elektrojupp/AD9954_TESTBOARD/pictures/IMG_0599.jpg

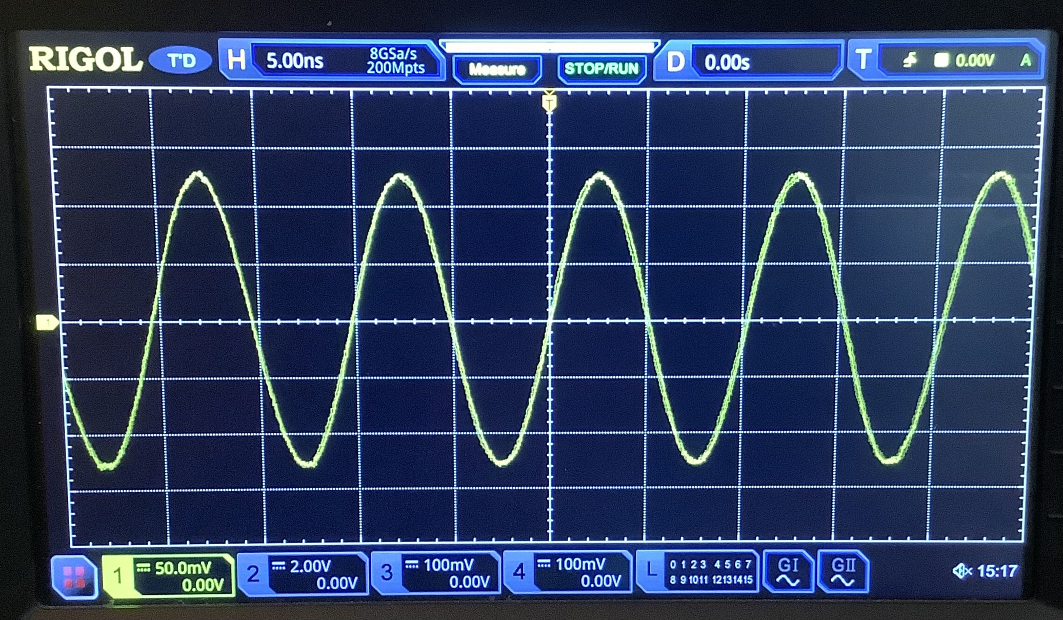
pictures/IMG_0599.jpg
