elektrojupp/AD9954_TESTBOARD/pictures/IMG_E0605.JPG

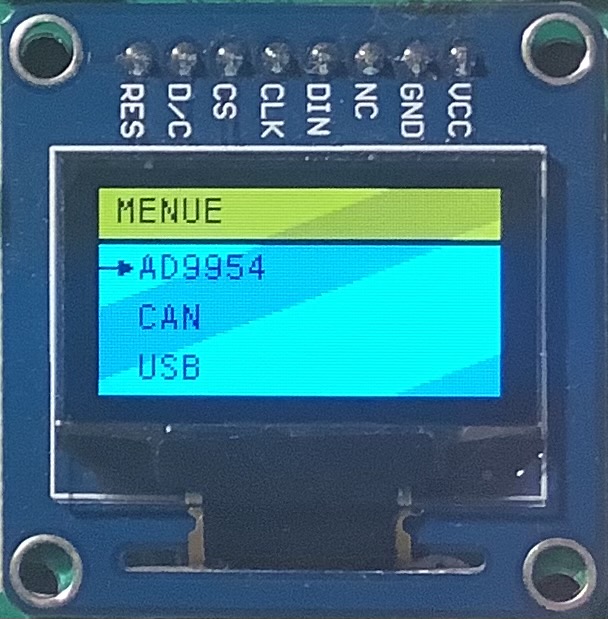
pictures/IMG_E0605.JPG
