elektrojupp/AD9954_TESTBOARD/pictures/IMG_E0612.JPG

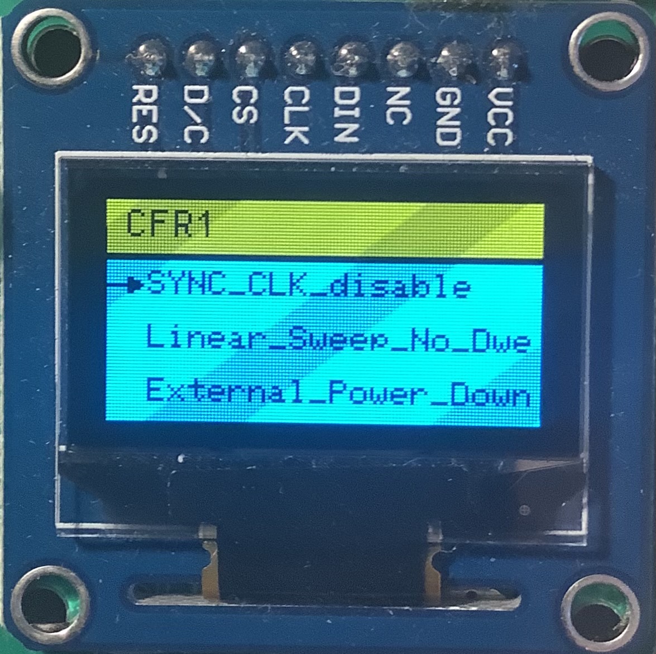
pictures/IMG_E0612.JPG
