elektrojupp/AD9954_TESTBOARD/pictures/IMG_E0613.JPG

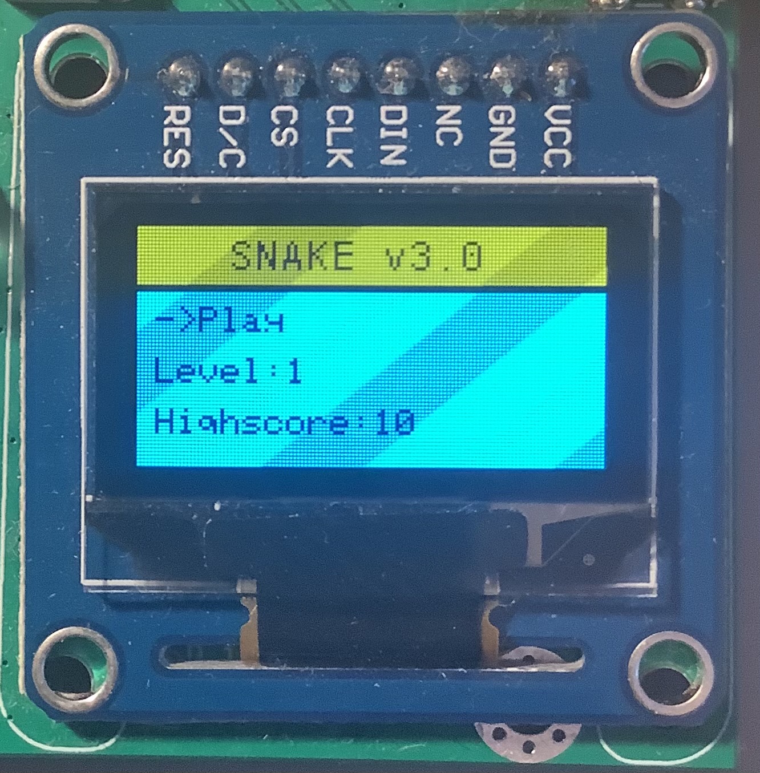
pictures/IMG_E0613.JPG
