elektrojupp/AD9954_TESTBOARD/pictures/IMG_E0616.JPG

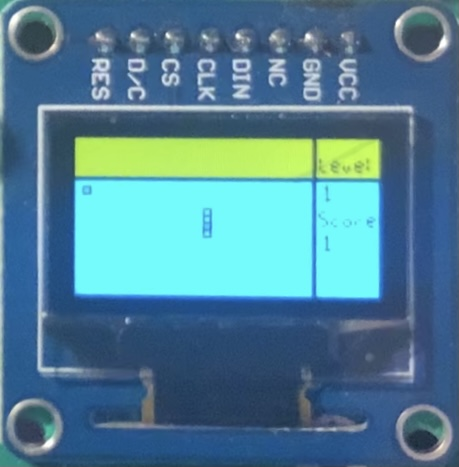
pictures/IMG_E0616.JPG
