elektrojupp/AD9954_TESTBOARD/pictures/IMG_E0635.JPG

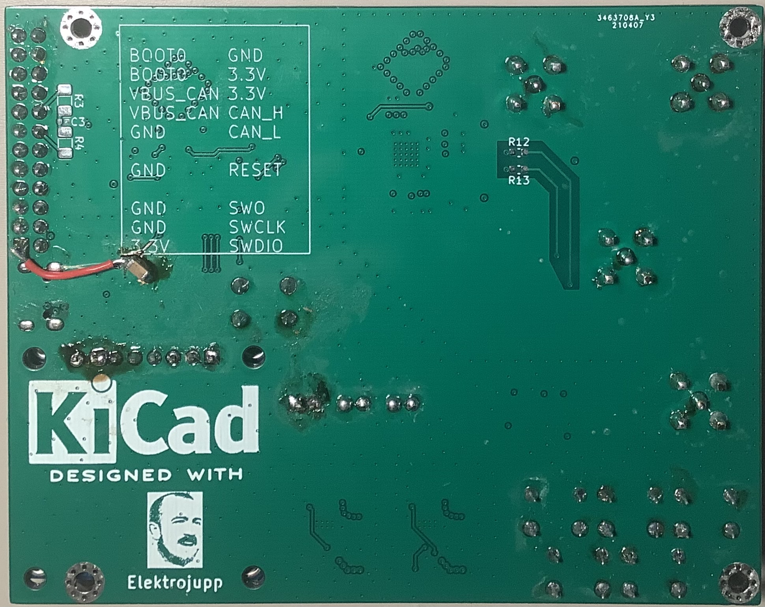
pictures/IMG_E0635.JPG
