elektrojupp/AD9954_TESTBOARD/software/Core/Inc/eeprom.h

#ifndef __EEPROM_H
#define __EEPROM_H

#ifdef __cplusplus
extern "C" {
#endif

#include <inttypes.h>

void EEPROM_Read(uint8_t adr, uint8_t * data, uint8_t size);
void EEPROM_Write(uint16_t adr, uint8_t * values, uint16_t size);



// FIRST BANK

#define ADDR_FLASH_PAGE_0     ((uint32_t)0x08000000) /* Base @ of Page 0, 2 Kbytes */
#define ADDR_FLASH_PAGE_1     ((uint32_t)0x08000800) /* Base @ of Page 1, 2 Kbytes */
#define ADDR_FLASH_PAGE_2     ((uint32_t)0x08001000) /* Base @ of Page 2, 2 Kbytes */
#define ADDR_FLASH_PAGE_3     ((uint32_t)0x08001800) /* Base @ of Page 3, 2 Kbytes */
#define ADDR_FLASH_PAGE_4     ((uint32_t)0x08002000) /* Base @ of Page 4, 2 Kbytes */
#define ADDR_FLASH_PAGE_5     ((uint32_t)0x08002800) /* Base @ of Page 5, 2 Kbytes */
#define ADDR_FLASH_PAGE_6     ((uint32_t)0x08003000) /* Base @ of Page 6, 2 Kbytes */
#define ADDR_FLASH_PAGE_7     ((uint32_t)0x08003800) /* Base @ of Page 7, 2 Kbytes */
#define ADDR_FLASH_PAGE_8     ((uint32_t)0x08004000) /* Base @ of Page 8, 2 Kbytes */
#define ADDR_FLASH_PAGE_9     ((uint32_t)0x08004800) /* Base @ of Page 9, 2 Kbytes */
#define ADDR_FLASH_PAGE_10     ((uint32_t)0x08005000) /* Base @ of Page 10, 2 Kbytes */
#define ADDR_FLASH_PAGE_11     ((uint32_t)0x08005800) /* Base @ of Page 11, 2 Kbytes */
#define ADDR_FLASH_PAGE_12     ((uint32_t)0x08006000) /* Base @ of Page 12, 2 Kbytes */
#define ADDR_FLASH_PAGE_13     ((uint32_t)0x08006800) /* Base @ of Page 13, 2 Kbytes */
#define ADDR_FLASH_PAGE_14     ((uint32_t)0x08007000) /* Base @ of Page 14, 2 Kbytes */
#define ADDR_FLASH_PAGE_15     ((uint32_t)0x08007800) /* Base @ of Page 15, 2 Kbytes */
#define ADDR_FLASH_PAGE_16     ((uint32_t)0x08008000) /* Base @ of Page 16, 2 Kbytes */
#define ADDR_FLASH_PAGE_17     ((uint32_t)0x08008800) /* Base @ of Page 17, 2 Kbytes */
#define ADDR_FLASH_PAGE_18     ((uint32_t)0x08009000) /* Base @ of Page 18, 2 Kbytes */
#define ADDR_FLASH_PAGE_19     ((uint32_t)0x08009800) /* Base @ of Page 19, 2 Kbytes */
#define ADDR_FLASH_PAGE_20     ((uint32_t)0x0800a000) /* Base @ of Page 20, 2 Kbytes */
#define ADDR_FLASH_PAGE_21     ((uint32_t)0x0800a800) /* Base @ of Page 21, 2 Kbytes */
#define ADDR_FLASH_PAGE_22     ((uint32_t)0x0800b000) /* Base @ of Page 22, 2 Kbytes */
#define ADDR_FLASH_PAGE_23     ((uint32_t)0x0800b800) /* Base @ of Page 23, 2 Kbytes */
#define ADDR_FLASH_PAGE_24     ((uint32_t)0x0800c000) /* Base @ of Page 24, 2 Kbytes */
#define ADDR_FLASH_PAGE_25     ((uint32_t)0x0800c800) /* Base @ of Page 25, 2 Kbytes */
#define ADDR_FLASH_PAGE_26     ((uint32_t)0x0800d000) /* Base @ of Page 26, 2 Kbytes */
#define ADDR_FLASH_PAGE_27     ((uint32_t)0x0800d800) /* Base @ of Page 27, 2 Kbytes */
#define ADDR_FLASH_PAGE_28     ((uint32_t)0x0800e000) /* Base @ of Page 28, 2 Kbytes */
#define ADDR_FLASH_PAGE_29     ((uint32_t)0x0800e800) /* Base @ of Page 29, 2 Kbytes */
#define ADDR_FLASH_PAGE_30     ((uint32_t)0x0800f000) /* Base @ of Page 30, 2 Kbytes */
#define ADDR_FLASH_PAGE_31     ((uint32_t)0x0800f800) /* Base @ of Page 31, 2 Kbytes */
#define ADDR_FLASH_PAGE_32     ((uint32_t)0x08010000) /* Base @ of Page 32, 2 Kbytes */
#define ADDR_FLASH_PAGE_33     ((uint32_t)0x08010800) /* Base @ of Page 33, 2 Kbytes */
#define ADDR_FLASH_PAGE_34     ((uint32_t)0x08011000) /* Base @ of Page 34, 2 Kbytes */
#define ADDR_FLASH_PAGE_35     ((uint32_t)0x08011800) /* Base @ of Page 35, 2 Kbytes */
#define ADDR_FLASH_PAGE_36     ((uint32_t)0x08012000) /* Base @ of Page 36, 2 Kbytes */
#define ADDR_FLASH_PAGE_37     ((uint32_t)0x08012800) /* Base @ of Page 37, 2 Kbytes */
#define ADDR_FLASH_PAGE_38     ((uint32_t)0x08013000) /* Base @ of Page 38, 2 Kbytes */
#define ADDR_FLASH_PAGE_39     ((uint32_t)0x08013800) /* Base @ of Page 39, 2 Kbytes */
#define ADDR_FLASH_PAGE_40     ((uint32_t)0x08014000) /* Base @ of Page 40, 2 Kbytes */
#define ADDR_FLASH_PAGE_41     ((uint32_t)0x08014800) /* Base @ of Page 41, 2 Kbytes */
#define ADDR_FLASH_PAGE_42     ((uint32_t)0x08015000) /* Base @ of Page 42, 2 Kbytes */
#define ADDR_FLASH_PAGE_43     ((uint32_t)0x08015800) /* Base @ of Page 43, 2 Kbytes */
#define ADDR_FLASH_PAGE_44     ((uint32_t)0x08016000) /* Base @ of Page 44, 2 Kbytes */
#define ADDR_FLASH_PAGE_45     ((uint32_t)0x08016800) /* Base @ of Page 45, 2 Kbytes */
#define ADDR_FLASH_PAGE_46     ((uint32_t)0x08017000) /* Base @ of Page 46, 2 Kbytes */
#define ADDR_FLASH_PAGE_47     ((uint32_t)0x08017800) /* Base @ of Page 47, 2 Kbytes */
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
#define ADDR_FLASH_PAGE_228     ((uint32_t)0x08072000) /* Base @ of Page 228, 2 Kbytes */
#define ADDR_FLASH_PAGE_229     ((uint32_t)0x08072800) /* Base @ of Page 229, 2 Kbytes */
#define ADDR_FLASH_PAGE_230     ((uint32_t)0x08073000) /* Base @ of Page 230, 2 Kbytes */
#define ADDR_FLASH_PAGE_231     ((uint32_t)0x08073800) /* Base @ of Page 231, 2 Kbytes */
#define ADDR_FLASH_PAGE_232     ((uint32_t)0x08074000) /* Base @ of Page 232, 2 Kbytes */
#define ADDR_FLASH_PAGE_233     ((uint32_t)0x08074800) /* Base @ of Page 233, 2 Kbytes */
#define ADDR_FLASH_PAGE_234     ((uint32_t)0x08075000) /* Base @ of Page 234, 2 Kbytes */
#define ADDR_FLASH_PAGE_235     ((uint32_t)0x08075800) /* Base @ of Page 235, 2 Kbytes */
#define ADDR_FLASH_PAGE_236     ((uint32_t)0x08076000) /* Base @ of Page 236, 2 Kbytes */
#define ADDR_FLASH_PAGE_237     ((uint32_t)0x08076800) /* Base @ of Page 237, 2 Kbytes */
#define ADDR_FLASH_PAGE_238     ((uint32_t)0x08077000) /* Base @ of Page 238, 2 Kbytes */
#define ADDR_FLASH_PAGE_239     ((uint32_t)0x08077800) /* Base @ of Page 239, 2 Kbytes */
#define ADDR_FLASH_PAGE_240     ((uint32_t)0x08078000) /* Base @ of Page 240, 2 Kbytes */
#define ADDR_FLASH_PAGE_241     ((uint32_t)0x08078800) /* Base @ of Page 241, 2 Kbytes */
#define ADDR_FLASH_PAGE_242     ((uint32_t)0x08079000) /* Base @ of Page 242, 2 Kbytes */
#define ADDR_FLASH_PAGE_243     ((uint32_t)0x08079800) /* Base @ of Page 243, 2 Kbytes */
#define ADDR_FLASH_PAGE_244     ((uint32_t)0x0807a000) /* Base @ of Page 244, 2 Kbytes */
#define ADDR_FLASH_PAGE_245     ((uint32_t)0x0807a800) /* Base @ of Page 245, 2 Kbytes */
#define ADDR_FLASH_PAGE_246     ((uint32_t)0x0807b000) /* Base @ of Page 246, 2 Kbytes */
#define ADDR_FLASH_PAGE_247     ((uint32_t)0x0807b800) /* Base @ of Page 247, 2 Kbytes */
#define ADDR_FLASH_PAGE_248     ((uint32_t)0x0807c000) /* Base @ of Page 248, 2 Kbytes */
#define ADDR_FLASH_PAGE_249     ((uint32_t)0x0807c800) /* Base @ of Page 249, 2 Kbytes */
#define ADDR_FLASH_PAGE_250     ((uint32_t)0x0807d000) /* Base @ of Page 250, 2 Kbytes */
#define ADDR_FLASH_PAGE_251     ((uint32_t)0x0807d800) /* Base @ of Page 251, 2 Kbytes */
#define ADDR_FLASH_PAGE_252     ((uint32_t)0x0807e000) /* Base @ of Page 252, 2 Kbytes */
#define ADDR_FLASH_PAGE_253     ((uint32_t)0x0807e800) /* Base @ of Page 253, 2 Kbytes */
#define ADDR_FLASH_PAGE_254     ((uint32_t)0x0807f000) /* Base @ of Page 254, 2 Kbytes */
#define ADDR_FLASH_PAGE_255     ((uint32_t)0x0807f800) /* Base @ of Page 255, 2 Kbytes */

// SECOND BANK

#define ADDR_FLASH_PAGE_256     ((uint32_t)0x08080000) /* Base @ of Page 256, 2 Kbytes */
#define ADDR_FLASH_PAGE_257     ((uint32_t)0x08080800) /* Base @ of Page 257, 2 Kbytes */
#define ADDR_FLASH_PAGE_258     ((uint32_t)0x08081000) /* Base @ of Page 258, 2 Kbytes */
#define ADDR_FLASH_PAGE_259     ((uint32_t)0x08081800) /* Base @ of Page 259, 2 Kbytes */
#define ADDR_FLASH_PAGE_260     ((uint32_t)0x08082000) /* Base @ of Page 260, 2 Kbytes */
#define ADDR_FLASH_PAGE_261     ((uint32_t)0x08082800) /* Base @ of Page 261, 2 Kbytes */
#define ADDR_FLASH_PAGE_262     ((uint32_t)0x08083000) /* Base @ of Page 262, 2 Kbytes */
#define ADDR_FLASH_PAGE_263     ((uint32_t)0x08083800) /* Base @ of Page 263, 2 Kbytes */
#define ADDR_FLASH_PAGE_264     ((uint32_t)0x08084000) /* Base @ of Page 264, 2 Kbytes */
#define ADDR_FLASH_PAGE_265     ((uint32_t)0x08084800) /* Base @ of Page 265, 2 Kbytes */
#define ADDR_FLASH_PAGE_266     ((uint32_t)0x08085000) /* Base @ of Page 266, 2 Kbytes */
#define ADDR_FLASH_PAGE_267     ((uint32_t)0x08085800) /* Base @ of Page 267, 2 Kbytes */
#define ADDR_FLASH_PAGE_268     ((uint32_t)0x08086000) /* Base @ of Page 268, 2 Kbytes */
#define ADDR_FLASH_PAGE_269     ((uint32_t)0x08086800) /* Base @ of Page 269, 2 Kbytes */
#define ADDR_FLASH_PAGE_270     ((uint32_t)0x08087000) /* Base @ of Page 270, 2 Kbytes */
#define ADDR_FLASH_PAGE_271     ((uint32_t)0x08087800) /* Base @ of Page 271, 2 Kbytes */
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
#define ADDR_FLASH_PAGE_484     ((uint32_t)0x080f2000) /* Base @ of Page 484, 2 Kbytes */
#define ADDR_FLASH_PAGE_485     ((uint32_t)0x080f2800) /* Base @ of Page 485, 2 Kbytes */
#define ADDR_FLASH_PAGE_486     ((uint32_t)0x080f3000) /* Base @ of Page 486, 2 Kbytes */
#define ADDR_FLASH_PAGE_487     ((uint32_t)0x080f3800) /* Base @ of Page 487, 2 Kbytes */
#define ADDR_FLASH_PAGE_488     ((uint32_t)0x080f4000) /* Base @ of Page 488, 2 Kbytes */
#define ADDR_FLASH_PAGE_489     ((uint32_t)0x080f4800) /* Base @ of Page 489, 2 Kbytes */
#define ADDR_FLASH_PAGE_490     ((uint32_t)0x080f5000) /* Base @ of Page 490, 2 Kbytes */
#define ADDR_FLASH_PAGE_491     ((uint32_t)0x080f5800) /* Base @ of Page 491, 2 Kbytes */
#define ADDR_FLASH_PAGE_492     ((uint32_t)0x080f6000) /* Base @ of Page 492, 2 Kbytes */
#define ADDR_FLASH_PAGE_493     ((uint32_t)0x080f6800) /* Base @ of Page 493, 2 Kbytes */
#define ADDR_FLASH_PAGE_494     ((uint32_t)0x080f7000) /* Base @ of Page 494, 2 Kbytes */
#define ADDR_FLASH_PAGE_495     ((uint32_t)0x080f7800) /* Base @ of Page 495, 2 Kbytes */
#define ADDR_FLASH_PAGE_496     ((uint32_t)0x080f8000) /* Base @ of Page 496, 2 Kbytes */
#define ADDR_FLASH_PAGE_497     ((uint32_t)0x080f8800) /* Base @ of Page 497, 2 Kbytes */
#define ADDR_FLASH_PAGE_498     ((uint32_t)0x080f9000) /* Base @ of Page 498, 2 Kbytes */
#define ADDR_FLASH_PAGE_499     ((uint32_t)0x080f9800) /* Base @ of Page 499, 2 Kbytes */
#define ADDR_FLASH_PAGE_500     ((uint32_t)0x080fa000) /* Base @ of Page 500, 2 Kbytes */
#define ADDR_FLASH_PAGE_501     ((uint32_t)0x080fa800) /* Base @ of Page 501, 2 Kbytes */
#define ADDR_FLASH_PAGE_502     ((uint32_t)0x080fb000) /* Base @ of Page 502, 2 Kbytes */
#define ADDR_FLASH_PAGE_503     ((uint32_t)0x080fb800) /* Base @ of Page 503, 2 Kbytes */
#define ADDR_FLASH_PAGE_504     ((uint32_t)0x080fc000) /* Base @ of Page 504, 2 Kbytes */
#define ADDR_FLASH_PAGE_505     ((uint32_t)0x080fc800) /* Base @ of Page 505, 2 Kbytes */
#define ADDR_FLASH_PAGE_506     ((uint32_t)0x080fd000) /* Base @ of Page 506, 2 Kbytes */
#define ADDR_FLASH_PAGE_507     ((uint32_t)0x080fd800) /* Base @ of Page 507, 2 Kbytes */
#define ADDR_FLASH_PAGE_508     ((uint32_t)0x080fe000) /* Base @ of Page 508, 2 Kbytes */
#define ADDR_FLASH_PAGE_509     ((uint32_t)0x080fe800) /* Base @ of Page 509, 2 Kbytes */
#define ADDR_FLASH_PAGE_510     ((uint32_t)0x080ff000) /* Base @ of Page 510, 2 Kbytes */
#define ADDR_FLASH_PAGE_511     ((uint32_t)0x080ff800) /* Base @ of Page 511, 2 Kbytes */

	//uint32_t x = 0;
	//uint32_t y = 0x08000000;
	//for(x = 0; x < 256; x ++)
	//{
	//	printf("#define ADDR_FLASH_PAGE_%ld     ((uint32_t)0x%08x) /* Base @ of Page %ld, 2 Kbytes */ \r\n", x, y, x);
	//	y = y + 0x800;
	//}
	//for(x = 256; x < 512; x ++)
	//{
	//	printf("#define ADDR_FLASH_PAGE_%ld     ((uint32_t)0x%08x) /* Base @ of Page %ld, 2 Kbytes */ \r\n", x, y, x);
	//	y = y + 0x800;
	//}
	//while(1);


#ifdef __cplusplus
}
#endif

#endif /* __BUTTON_H */
